v8355800/rx02_emulator/assets/adapter/RX02_Adapter_Case_Bottom.png

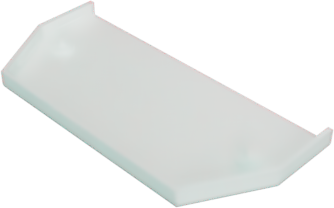
assets/adapter/RX02_Adapter_Case_Bottom.png
