v8355800/rx02_emulator/assets/emulator/RX02_Emulator_Case_Body_1.png

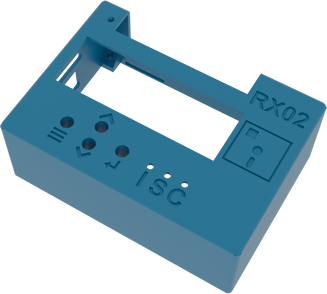
assets/emulator/RX02_Emulator_Case_Body_1.png
